joachim-reuter/ESP32-GPS-LoRaWAN-Tracker/_Little_FS_init.ino

#include <LittleFS.h>

void setup() {
  Serial.begin(115200);
  LittleFS.begin(true);

  File g = LittleFS.open("/intervall.txt", "w");  
  g.println("intervall=30");  
  g.close();

  Serial.println("OK geschrieben");
}

void loop() {}
